tinygo-keeb/tinygo-conf-2026-badge/firmware/examples/slotgame/img/tinygo.png

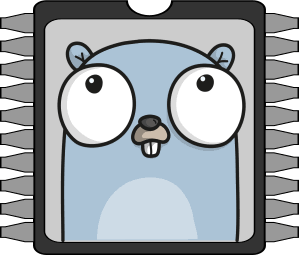
firmware/examples/slotgame/img/tinygo.png
