tinygo-keeb/tinygo-conf-2026-badge/hardware/build/img/part_list.jpg

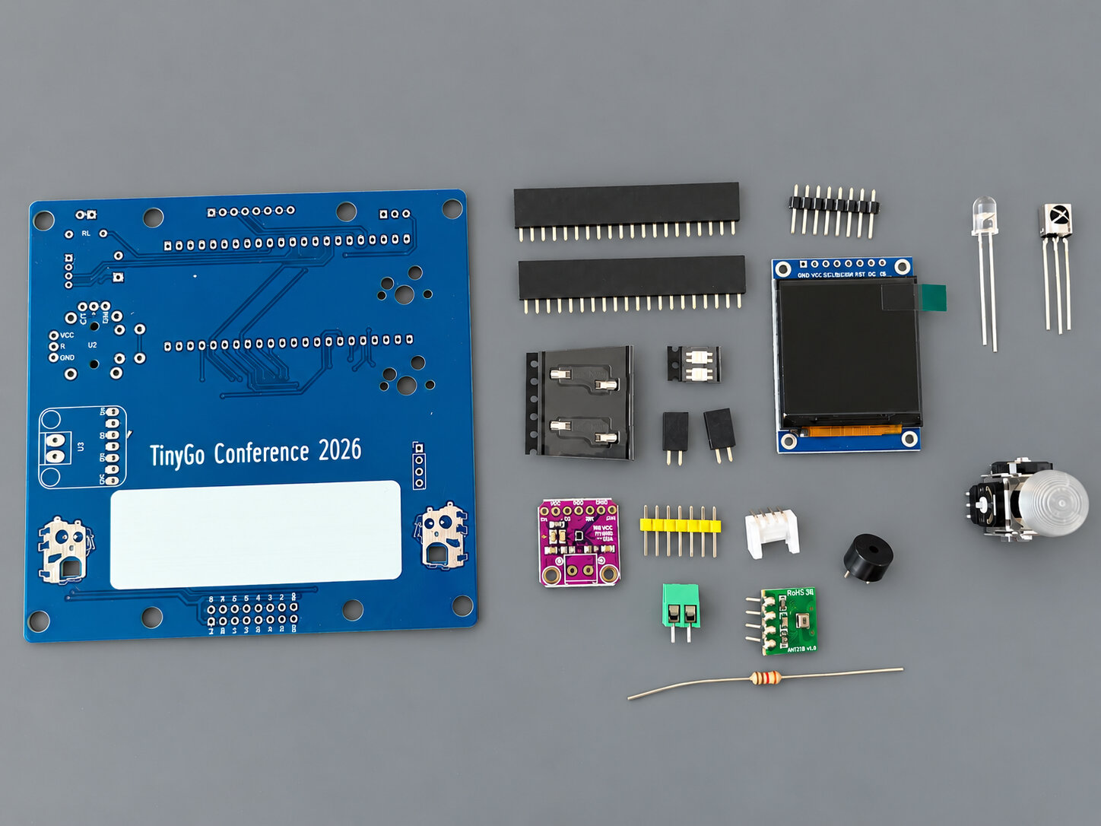
hardware/build/img/part_list.jpg
